jpskenn/Colice/assets/Colice_v.0.2_5.jpeg

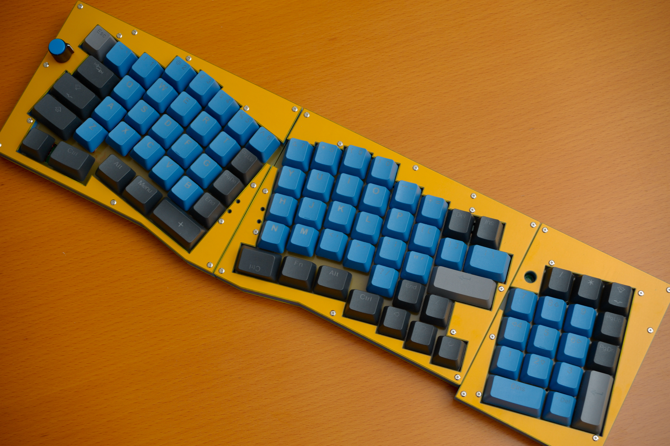
assets/Colice_v.0.2_5.jpeg
