jpskenn/Colice/assets/Colice_v.0.2_9.jpeg

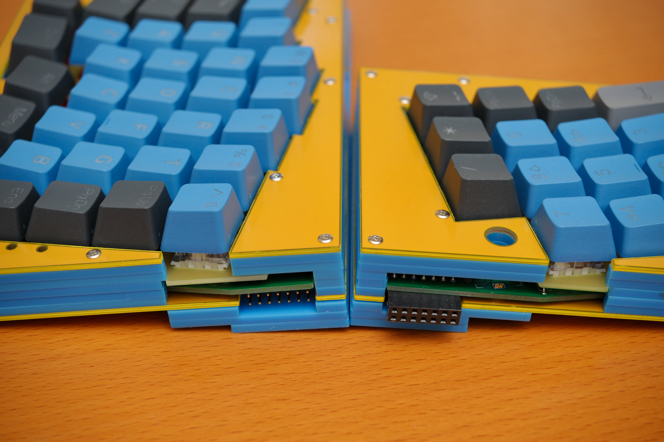
assets/Colice_v.0.2_9.jpeg
