jpskenn/Colice/assets/Colice_v.0.2_11.jpeg

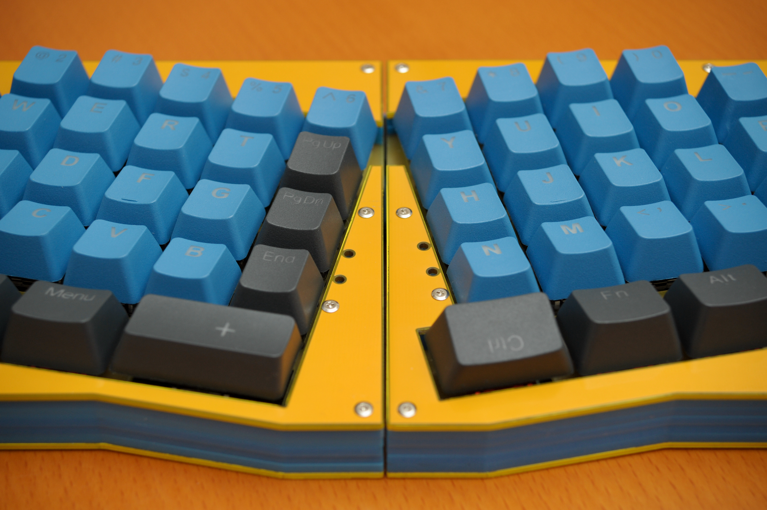
assets/Colice_v.0.2_11.jpeg
