jpskenn/Colice/idea/7w7xx1621ke41.jpg

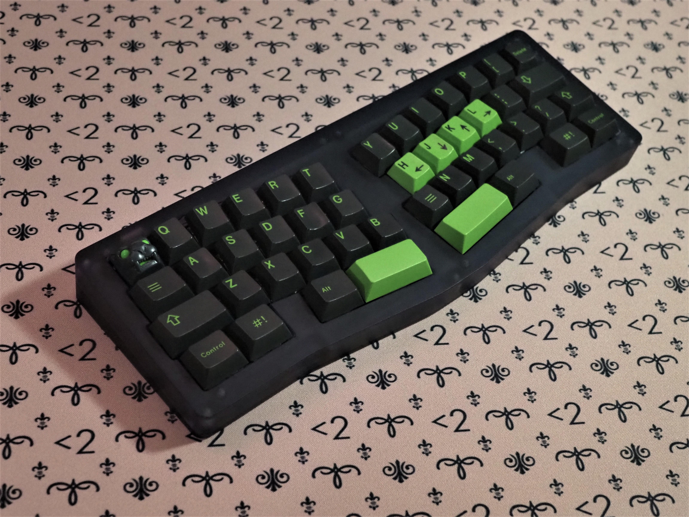
idea/7w7xx1621ke41.jpg
