jpskenn/Colice/idea/fullsizeoutput_168.jpeg

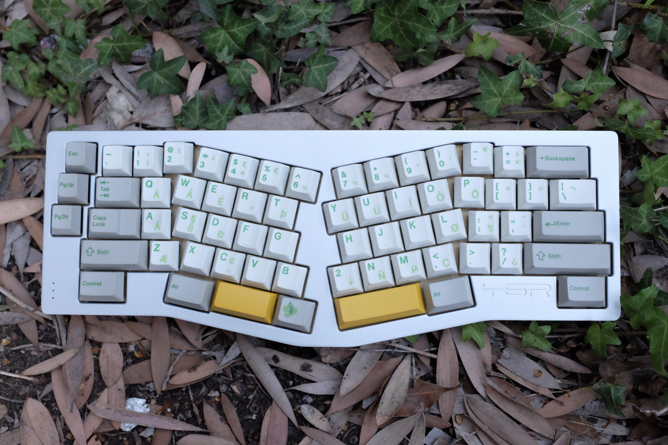
idea/fullsizeoutput_168.jpeg
