jpskenn/Colice/idea/IMG_0921.jpeg

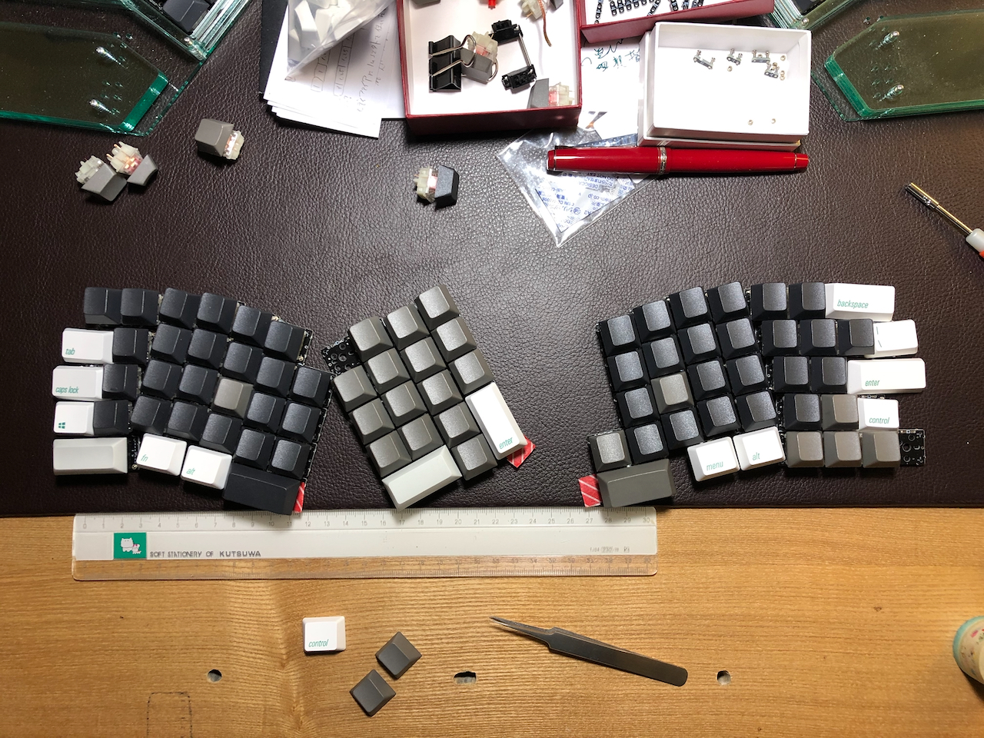
idea/IMG_0921.jpeg
