jpskenn/Colice/idea/IMG_0922.jpeg

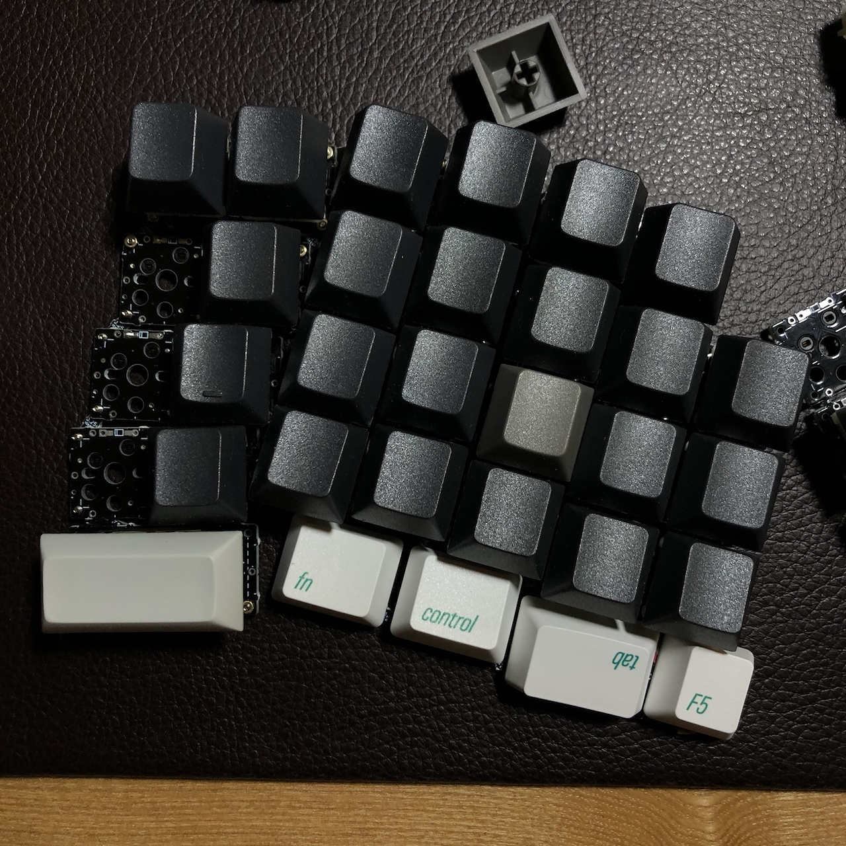
idea/IMG_0922.jpeg
