jpskenn/Colice/idea/keyboards_ergo_tgr-alice-layout-1024x415.png

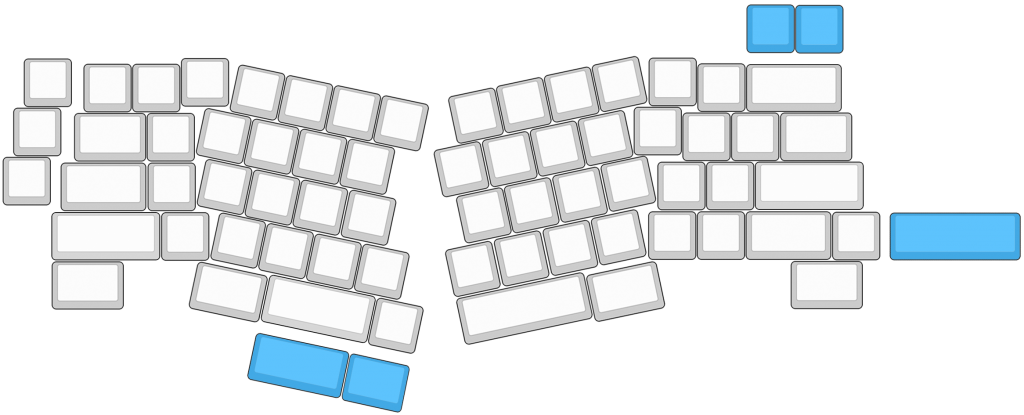
idea/keyboards_ergo_tgr-alice-layout-1024x415.png
