jpskenn/Colice/idea/Lain_by_hsgw.jpg

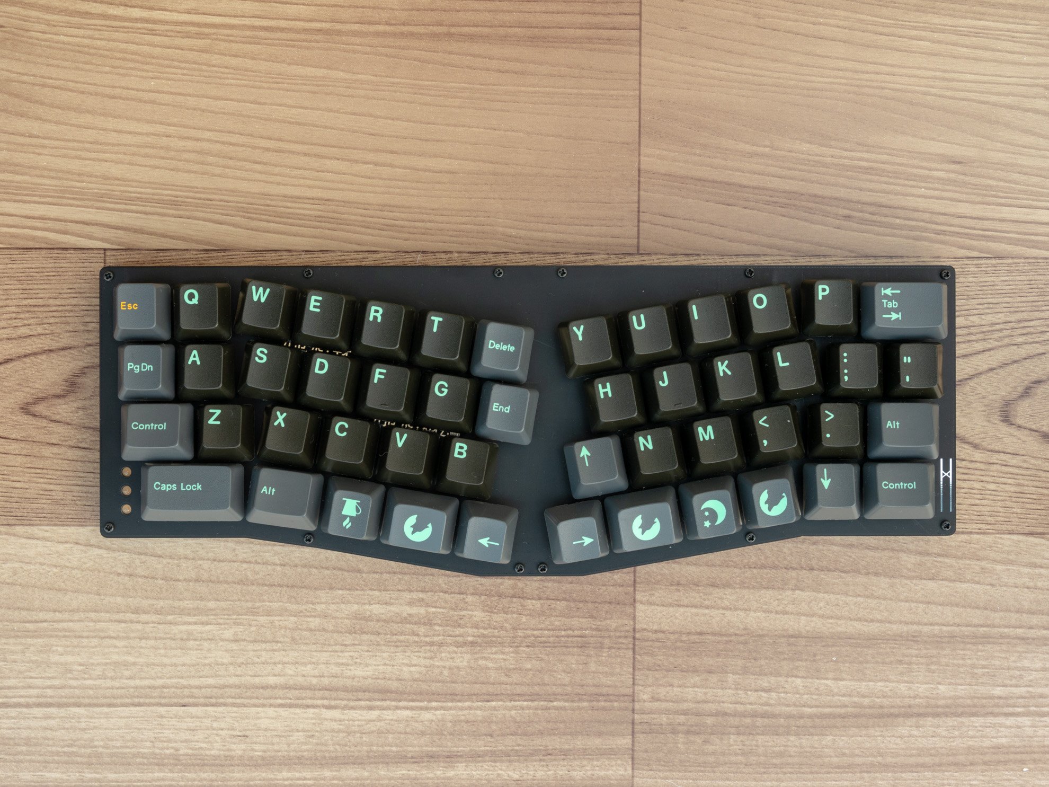
idea/Lain_by_hsgw.jpg
