jpskenn/Colice/idea/mainphoto.jpg

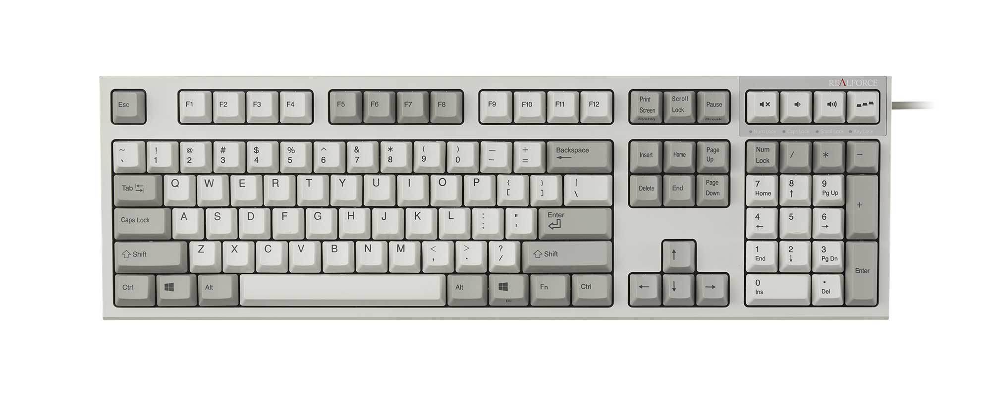
idea/mainphoto.jpg
