jpskenn/Colice/idea/uoq6nv9i2eb41 2.jpg

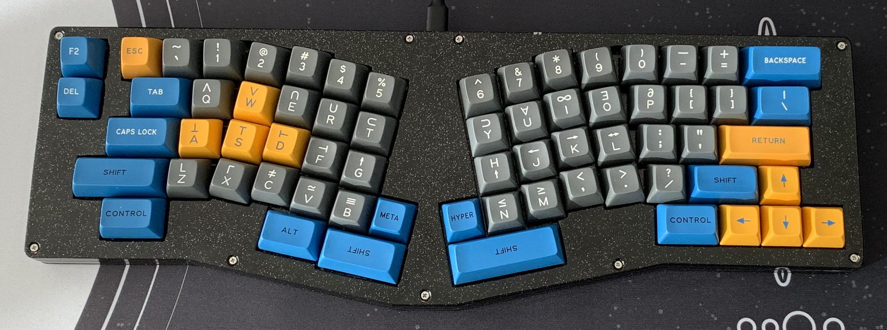
idea/uoq6nv9i2eb41 2.jpg
