jpskenn/Colice/idea/uoq6nv9i2eb41.jpg

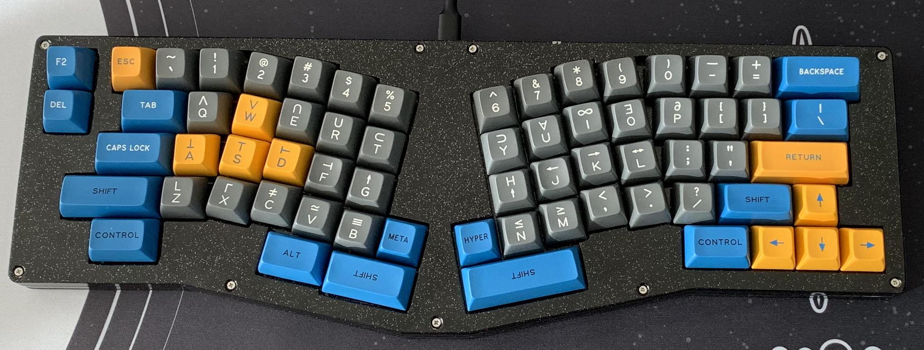
idea/uoq6nv9i2eb41.jpg
