jpskenn/Colice/idea/一体型分割3.jpg

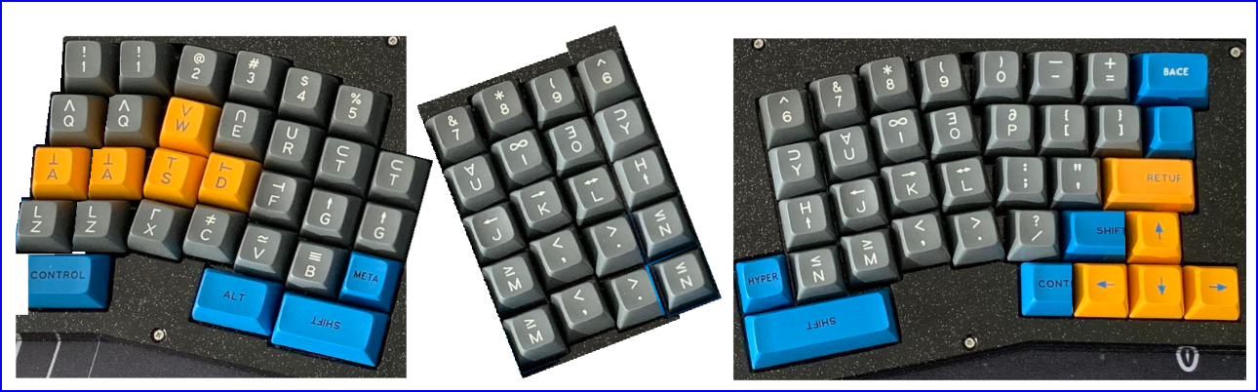
idea/一体型分割3.jpg
