jpskenn/Colice/PCB_Keyplate/v.0.1/left_keyplate2.dxf

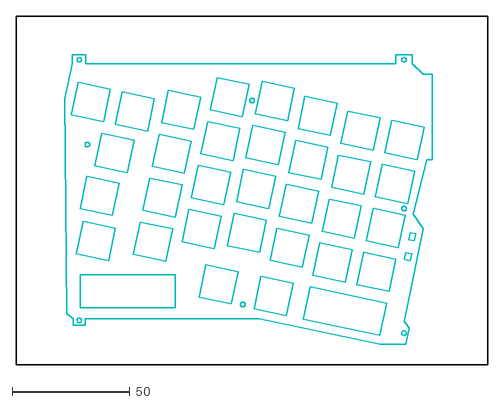
[picture p36: CAD file, 2025-01-15, an earlier design]
PCB_Keyplate/v.0.1/left_keyplate2.dxf
199.8 x 147.9
