jpskenn/Colice/PCB_MidFrame/v.0.1/left_mid.dxf

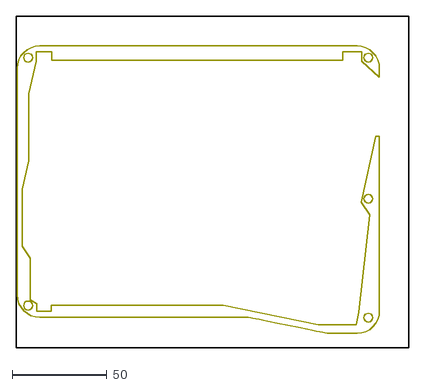
[picture p37: CAD file, 2025-01-15, an earlier design]
PCB_MidFrame/v.0.1/left_mid.dxf
207.4 x 175.2
