jpskenn/Colice/PCB_TopFrame/v.0.1/left_top2.dxf

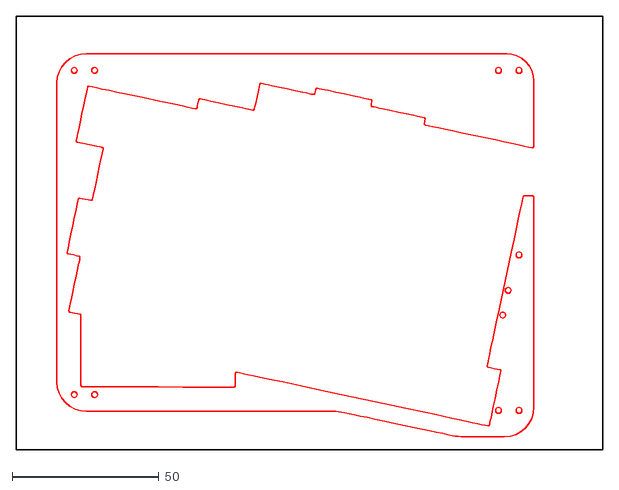
[picture p38: CAD file, 2025-01-15, an earlier design]
PCB_TopFrame/v.0.1/left_top2.dxf
199.8 x 147.9
