jpskenn/Colice/PCB_Bottom/v.0.1/left_bottom.dxf

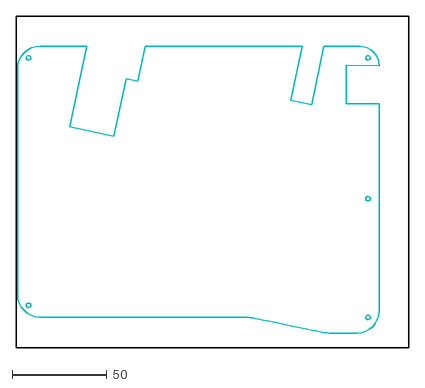
[picture p39: CAD file, 2025-01-15, an earlier design]
PCB_Bottom/v.0.1/left_bottom.dxf
207.4 x 175.2
