jpskenn/Colice/Case : Plate/3D Print/3dCase_test_2020-Feb-23_08-43-58AM-000_CustomizedView15799716209.png

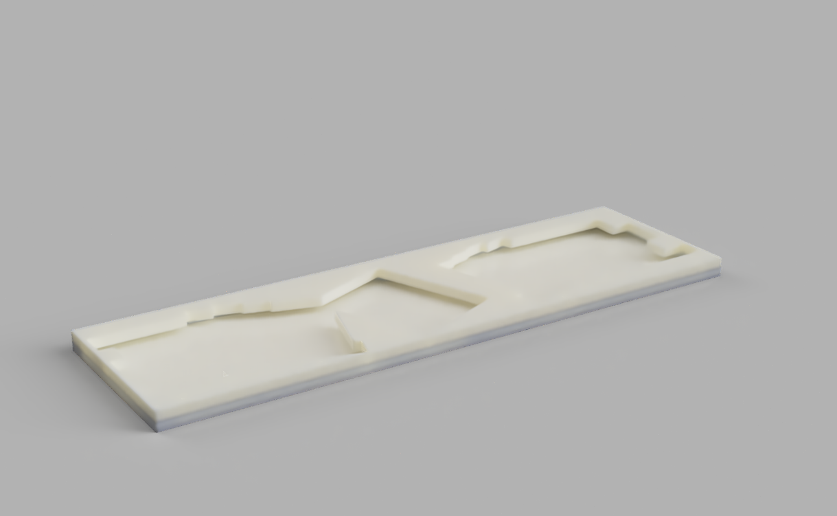
Case : Plate/3D Print/3dCase_test_2020-Feb-23_08-43-58AM-000_CustomizedView15799716209.png
