jpskenn/Colice/PCB/Num v.0.1/Colice_RR_Num_rev.0.1-003/Colice.kicad_pcb

## KiCad design PCB/Num v.0.1/Colice_RR_Num_rev.0.1-003/Colice.kicad_pcb (2025-01-15, an earlier design)

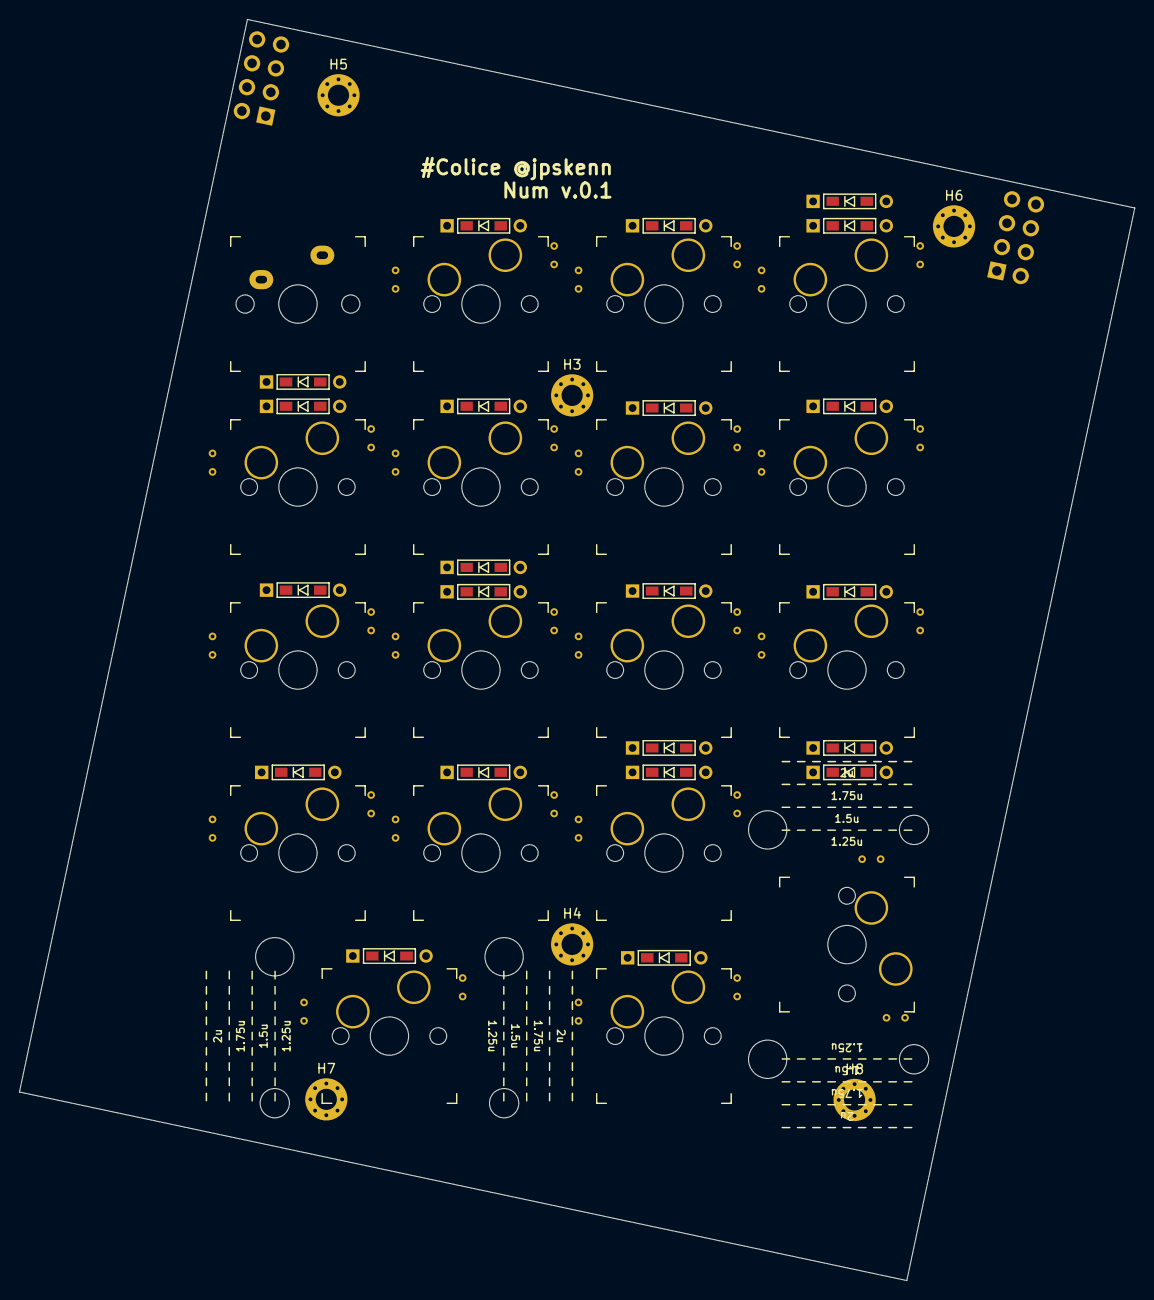
[picture p47: board PCB/Num v.0.1/Colice_RR_Num_rev.0.1-003/Colice.kicad_pcb from above]

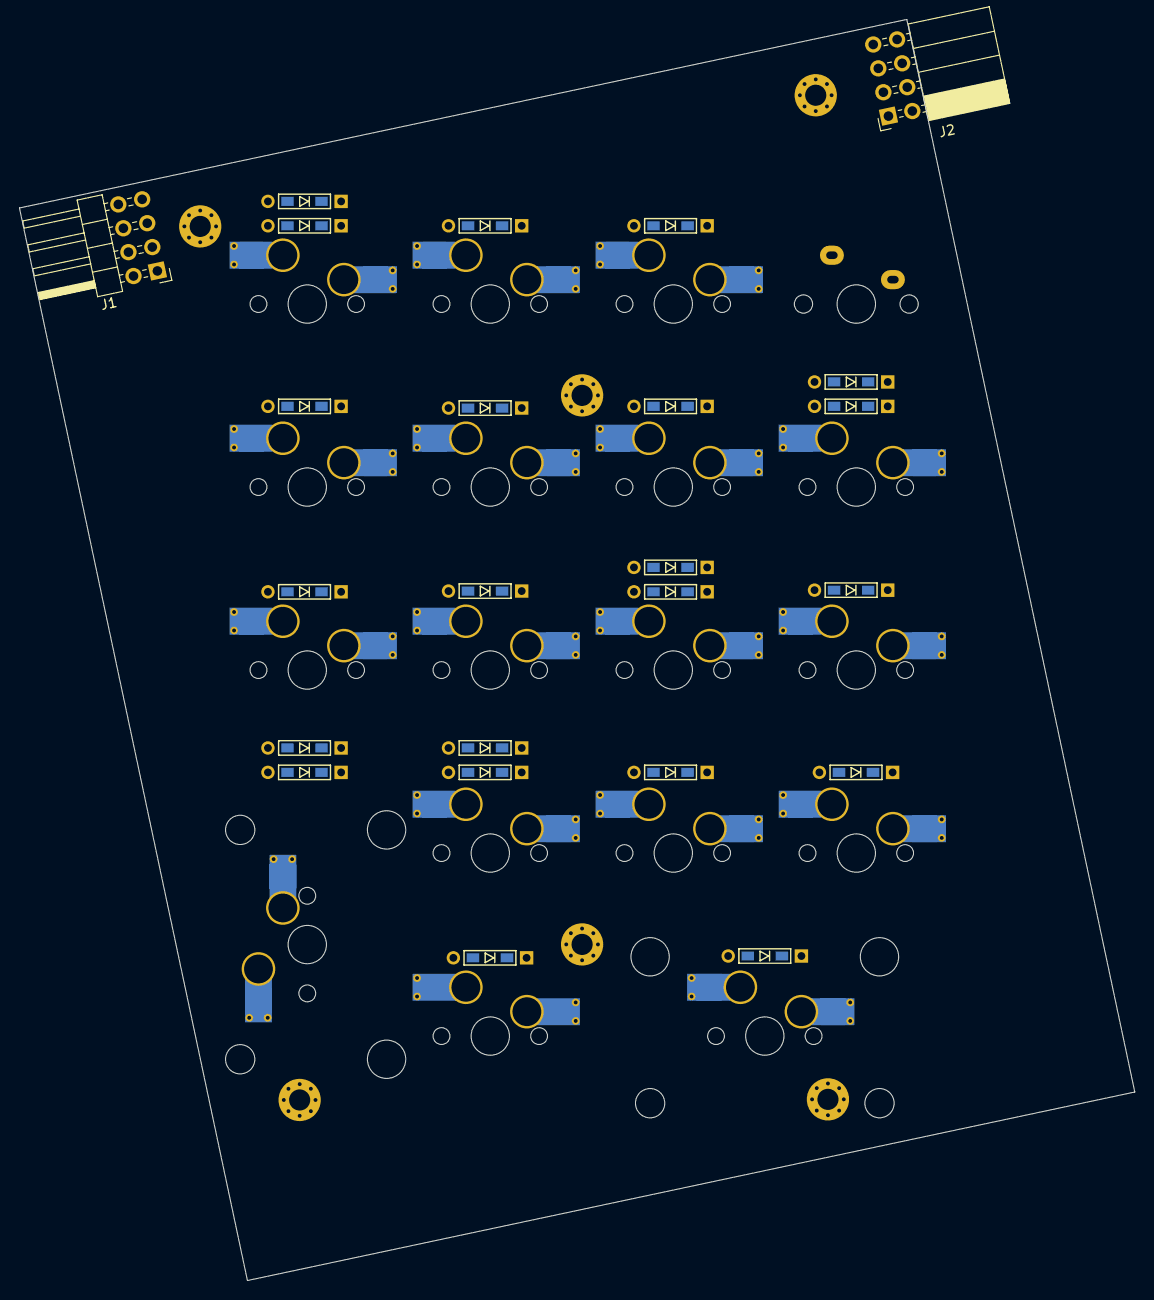
[picture p48: board PCB/Num v.0.1/Colice_RR_Num_rev.0.1-003/Colice.kicad_pcb from below]

Board: 2 copper layers, 116.1 x 131.3 mm, 50 parts (2 on the bottom side), 30 nets, no tracks yet.

Parts:
D1, D2, D3, D4, D5, D6, D7, D8, D9, D10, D11, D12, D13, D14, D15, D16, D17, D18, D19, D20, D21, D22: D; D3_TH_SMD
H1, H2: MountingHole; CherryMX_MidHeight_Choc_Hotswap_2U_Outline
H3, H4, H5, H6, H7, H8: MountingHole; MountingHole_2.2mm_M2_Pad_Via
J1: Conn_02x04_Counter_Clockwise; PinHeader_2x04_P2.54mm_Horizontal
J2: Conn_02x04_Counter_Clockwise; PinSocket_2x04_P2.54mm_Horizontal
SW1: SW_PUSH; CherryMX_1u
SW1#2, SW2, SW3, SW4, SW5, SW6, SW7, SW8, SW9, SW10, SW11, SW12, SW13, SW14, SW15, SW16, SW17: SW_Push; CherryMX_Hotswap_v2

Connections:
GND: J1.7, J2.7
unnamed: D1.2, SW1#2.2
unnamed: D2.2, SW2.2
unnamed: D3.2, SW3.2
unnamed: D4.2, SW4.2
unnamed: D5.2, SW5.2
unnamed: D6.2, SW6.2
unnamed: D7.2, SW7.2
unnamed: D8.2, SW8.2
unnamed: D9.2, SW9.2
unnamed: D10.2, SW10.2
unnamed: D11.2, SW11.2
unnamed: D12.2, SW12.2
unnamed: D13.2, SW13.2
unnamed: D14.2, SW14.2
unnamed: D15.2, SW15.2
unnamed: D16.2, SW16.2
unnamed: D17.2, SW17.2
unnamed: D18.1, SW14.1, SW15.1, SW16.1
unnamed: D19.1, SW1#2.1, SW2.1, SW3.1, SW4.1
unnamed: D20.1, SW7.1, SW8.1
unnamed: D21.1, SW5.1, SW6.1, SW12.1, SW13.1
unnamed: D22.1, SW9.1, SW10.1, SW11.1, SW17.1
VCC: J1.8, J2.8
data: J1.6, J2.6
pin6: D5.1, D9.1, D14.1, D19.2, J2.1
pin7: D1.1, D6.1, D10.1, D15.1, D20.2, J2.2
pin8: D2.1, D7.1, D11.1, D16.1, D21.2, J2.3
pin9: D3.1, D8.1, D12.1, D22.2, J2.4
pin10: D4.1, D13.1, D17.1, D18.2, J2.5
