jpskenn/Colice/PCB/Colice_rev.0.1/Colice_rev.0.1.kicad_pcb

## KiCad design PCB/Colice_rev.0.1/Colice_rev.0.1.kicad_pcb (2025-01-15)

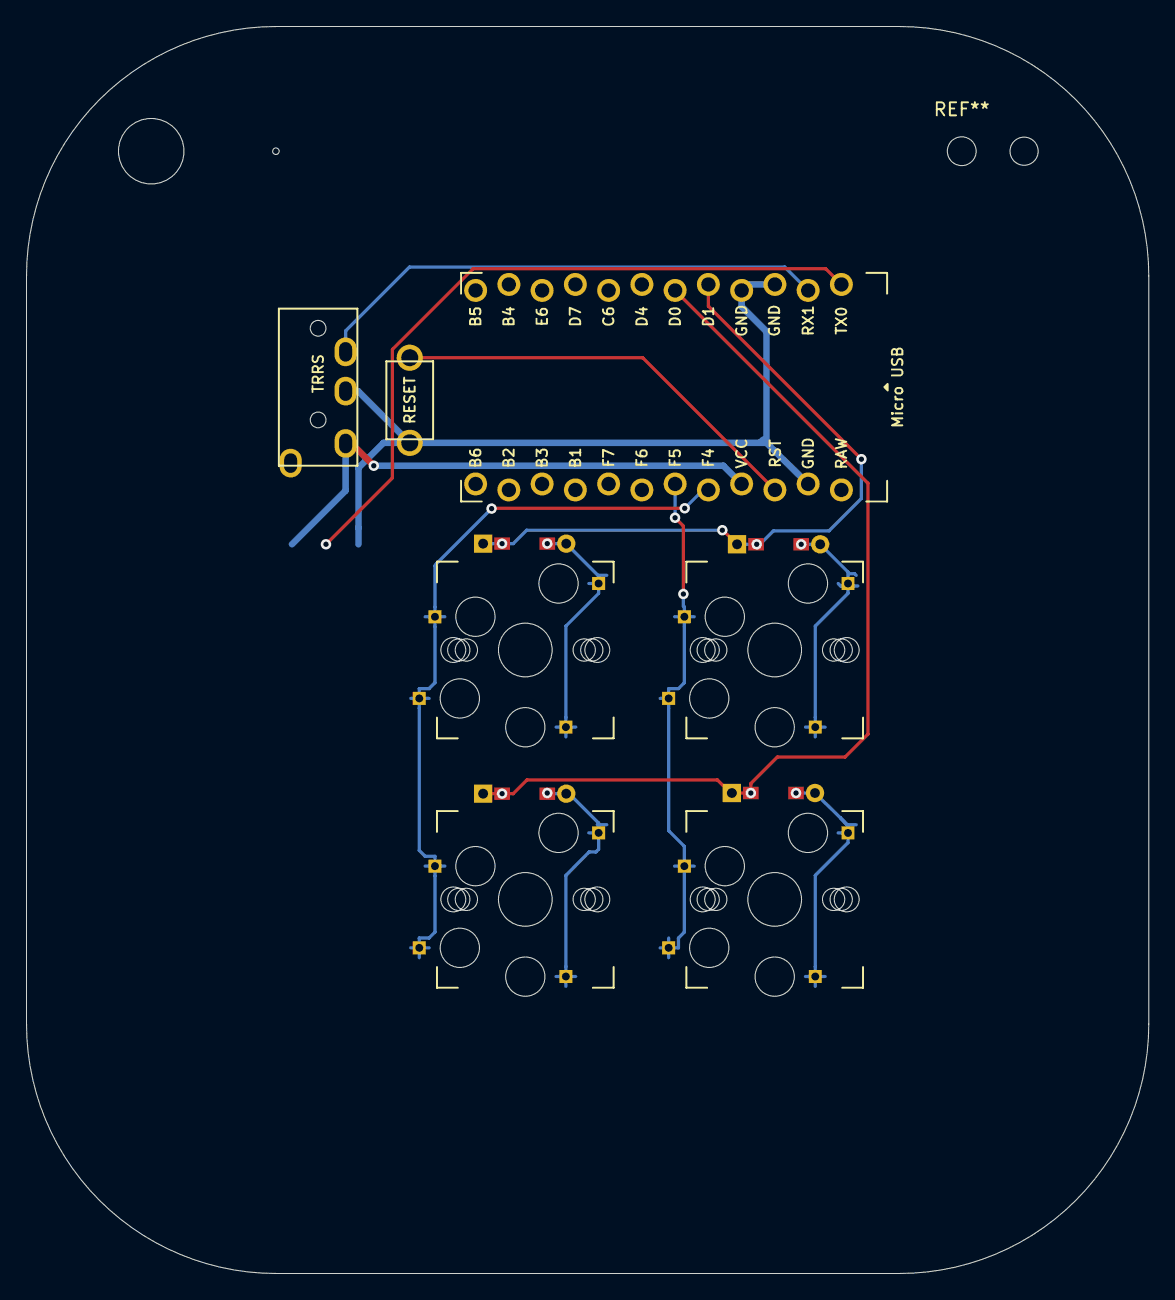
[picture p49: board Colice_rev.0.1.kicad_pcb from above]

Board: 2 copper layers, 85.7 x 95.2 mm, 13 parts (0 on the bottom side), 13 nets.

Parts:
D1, D2, D3, D4: D; diode_TH_SMD_rev2
J1: MJ-4PP-9
J2: LED; StripLED_rev2
Ref**: Val**; IM_HOLE
SW1: SW_Push; ResetSW
SW2, SW3, SW4, SW5: SW_Push; CherryMX_MidHeight_Choc_Hotswap_rev5
U1: pro_micro; ArduinoProMicro-ZigZag_rev5

Connections:
GND: J1.C, J2.1, SW1.2, U1.3, U1.4, U1.23
unnamed: D1.2, SW2.2
unnamed: D2.2, SW3.2
unnamed: D3.2, SW4.2
unnamed: D4.2, SW5.2
VCC: J1.D, J2.3, U1.21
col0: SW2.1, SW3.1, U1.20
col1: SW4.1, SW5.1, U1.19
data: J1.B, U1.2
led: J2.2, U1.1
reset: SW1.1, U1.22
row0: D1.1, D3.1, U1.5
row1: D2.1, D4.1, U1.6
