jpskenn/Colice/PCB/Num v.0.2/Colice_RR_Num_rev.0.2-001/Colice.kicad_pcb

## KiCad design PCB/Num v.0.2/Colice_RR_Num_rev.0.2-001/Colice.kicad_pcb (2025-01-15)

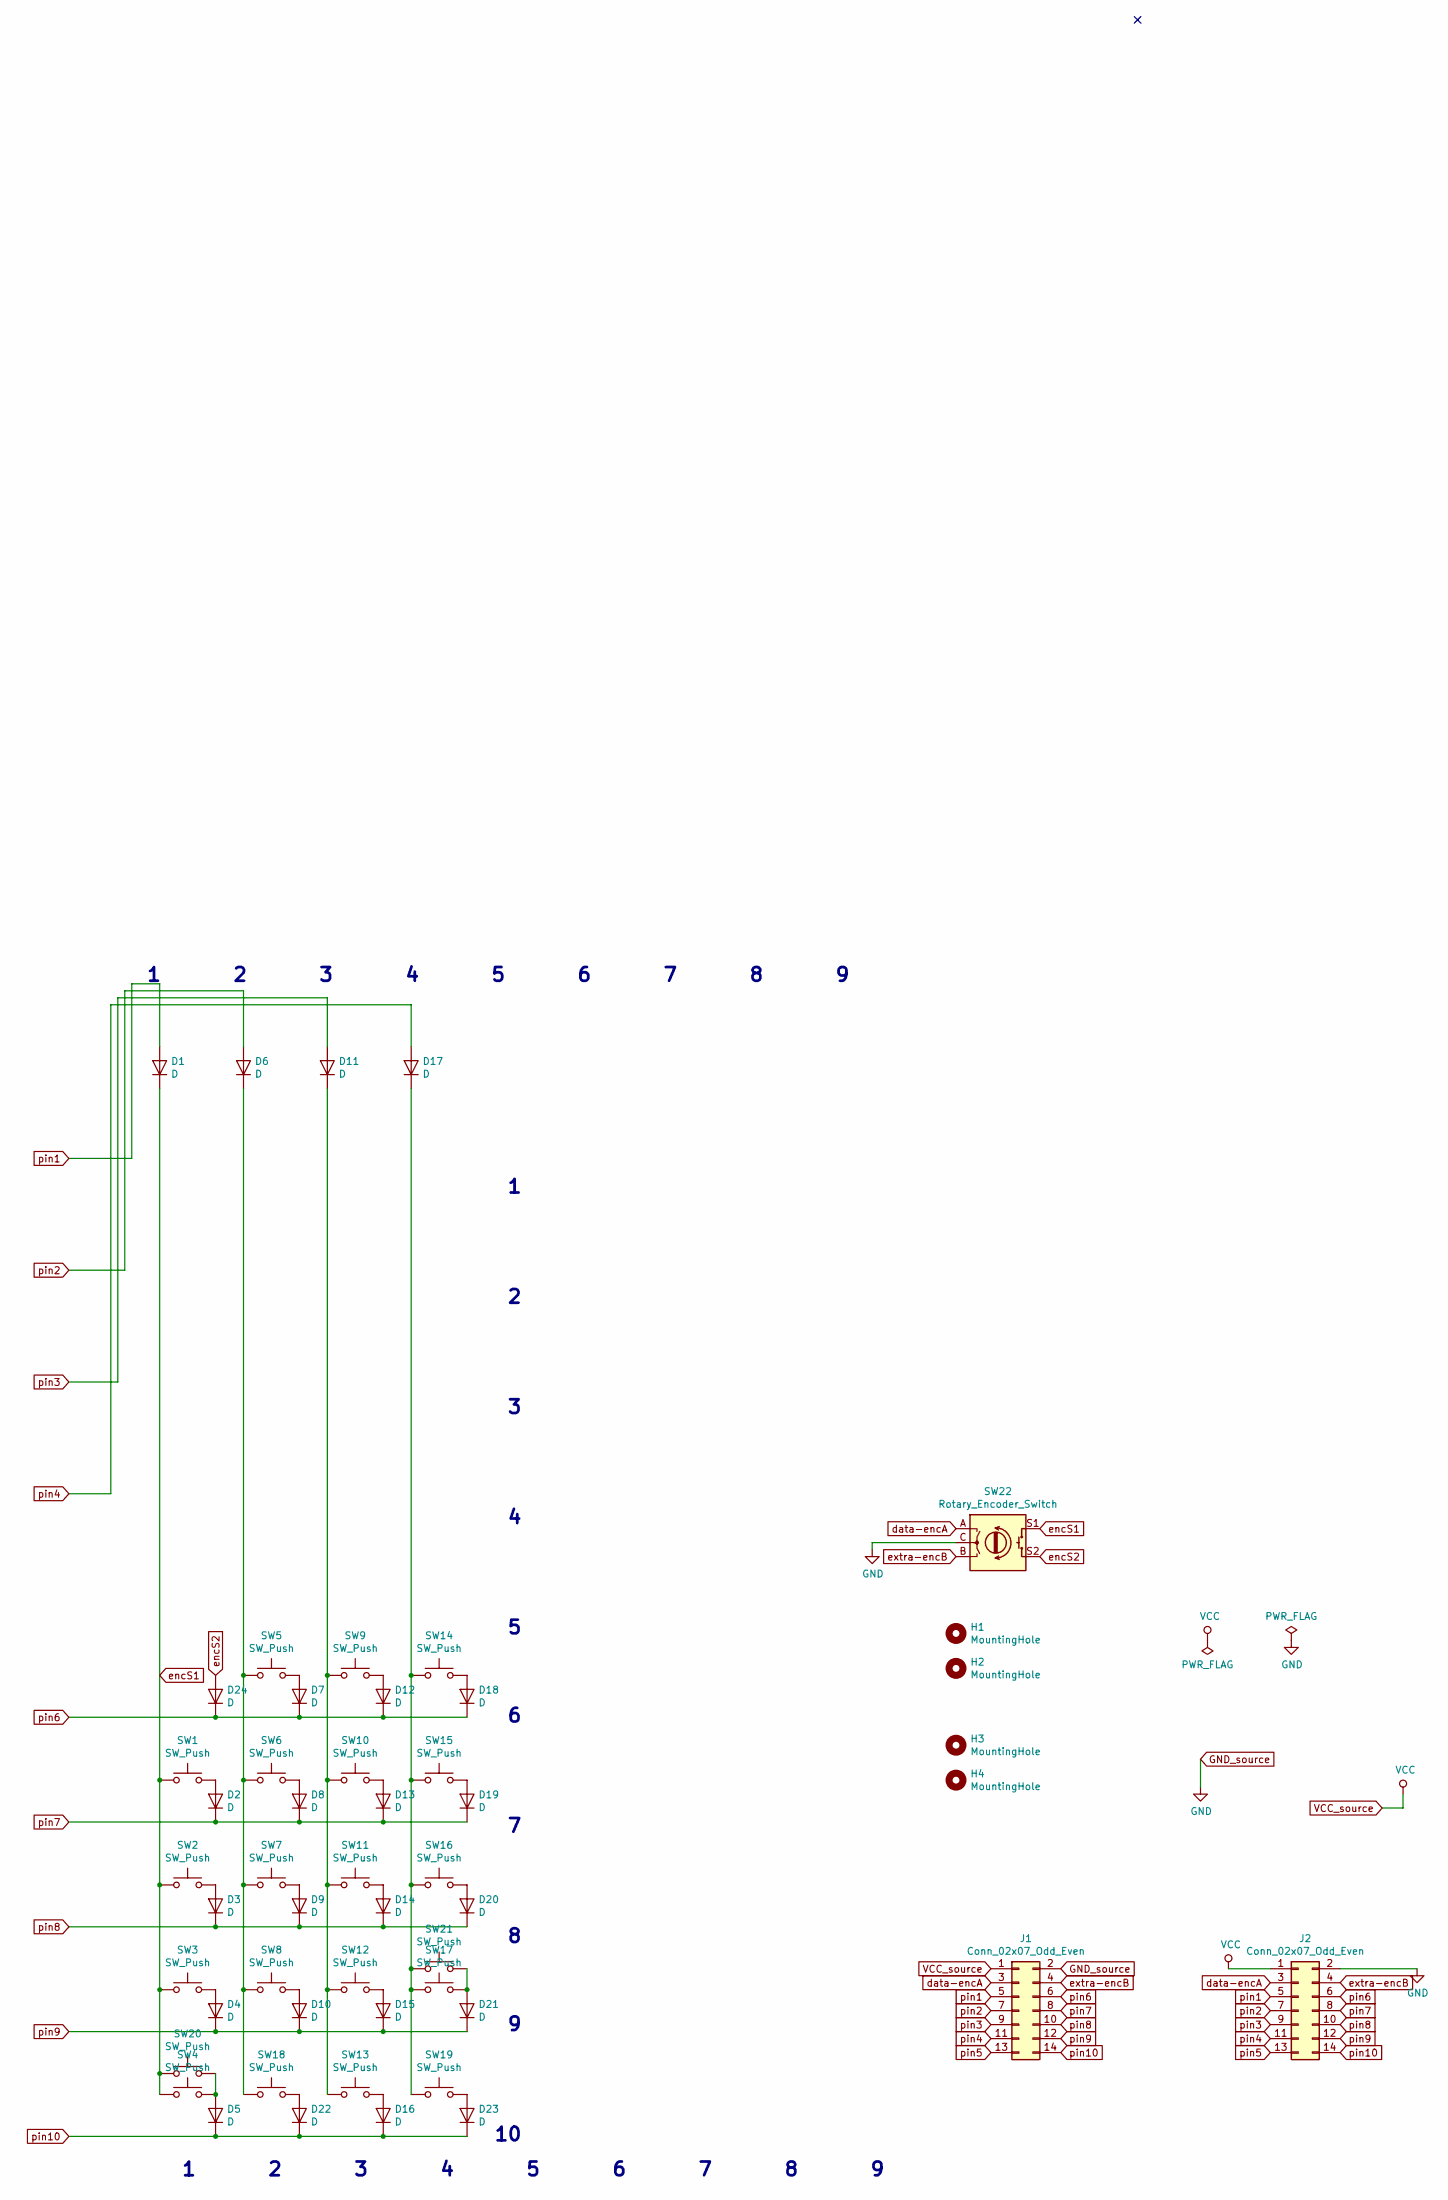
[picture p50: schematic Colice.sch]

Parts:
D1, D2, D3, D4, D5, D6, D7, D8, D9, D10, D11, D12, D13, D14, D15, D16, D17, D18, D19, D20, D21, D22, D23, D24: D; D3_TH_SMD
H1, H2: MountingHole; CherryMX_MidHeight_Choc_Hotswap_2U_Outline
H3, H4: MountingHole; MountingHole_2.2mm_M2_Pad_Via
J1: Conn_02x07_Odd_Even; PinSocket_2x07_P2.54mm_Horizontal
J2: Conn_02x07_Odd_Even; PinHeader_2x07_P2.54mm_Horizontal
SW1, SW2, SW3, SW4, SW5, SW6, SW7, SW8, SW9, SW10, SW11, SW12, SW13, SW14, SW15, SW16, SW17, SW18, SW19, SW20, SW21: SW_Push; CherryMX_Hotswap_v2
SW22: Rotary_Encoder_Switch; RotaryEncoder_Alps_EC11E-Switch_Vertical_H20mm_rev2

Connections:
GND_source: J1.2, J2.2, SW22.C
unnamed: D2.2 (A), SW1.2
unnamed: D3.2 (A), SW2.2
unnamed: D4.2 (A), SW3.2
unnamed: D5.2 (A), SW4.2, SW20.2
unnamed: D6.1 (K), SW5.1, SW6.1, SW7.1, SW8.1, SW18.1
unnamed: D7.2 (A), SW5.2
unnamed: D8.2 (A), SW6.2
unnamed: D9.2 (A), SW7.2
unnamed: D10.2 (A), SW8.2
unnamed: D11.1 (K), SW9.1, SW10.1, SW11.1, SW12.1, SW13.1
unnamed: D12.2 (A), SW9.2
unnamed: D13.2 (A), SW10.2
unnamed: D14.2 (A), SW11.2
unnamed: D15.2 (A), SW12.2
unnamed: D16.2 (A), SW13.2
unnamed: D17.1 (K), SW14.1, SW15.1, SW16.1, SW17.1, SW19.1, SW21.1
unnamed: D18.2 (A), SW14.2
unnamed: D19.2 (A), SW15.2
unnamed: D20.2 (A), SW16.2
unnamed: D21.2 (A), SW17.2, SW21.2
unnamed: D22.2 (A), SW18.2
unnamed: D23.2 (A), SW19.2
VCC_source: J1.1, J2.1
data-encA: J1.3, J2.3, SW22.A
encS1: D1.1 (K), SW1.1, SW2.1, SW3.1, SW4.1, SW20.1, SW22.S1
encS2: D24.2 (A), SW22.S2
extra-encB: J1.4, J2.4, SW22.B
pin1: D1.2 (A), J1.5, J2.5
pin2: D6.2 (A), J1.7, J2.7
pin3: D11.2 (A), J1.9, J2.9
pin4: D17.2 (A), J1.11, J2.11
pin5: J1.13, J2.13
pin6: D7.1 (K), D12.1 (K), D18.1 (K), D24.1 (K), J1.6, J2.6
pin7: D2.1 (K), D8.1 (K), D13.1 (K), D19.1 (K), J1.8, J2.8
pin8: D3.1 (K), D9.1 (K), D14.1 (K), D20.1 (K), J1.10, J2.10
pin9: D4.1 (K), D10.1 (K), D15.1 (K), D21.1 (K), J1.12, J2.12
pin10: D5.1 (K), D16.1 (K), D22.1 (K), D23.1 (K), J1.14, J2.14

Notes on the sheet:
1 2 3 4 5 6 7 8 9
1 2 3 4 5 6 7 8 9 10

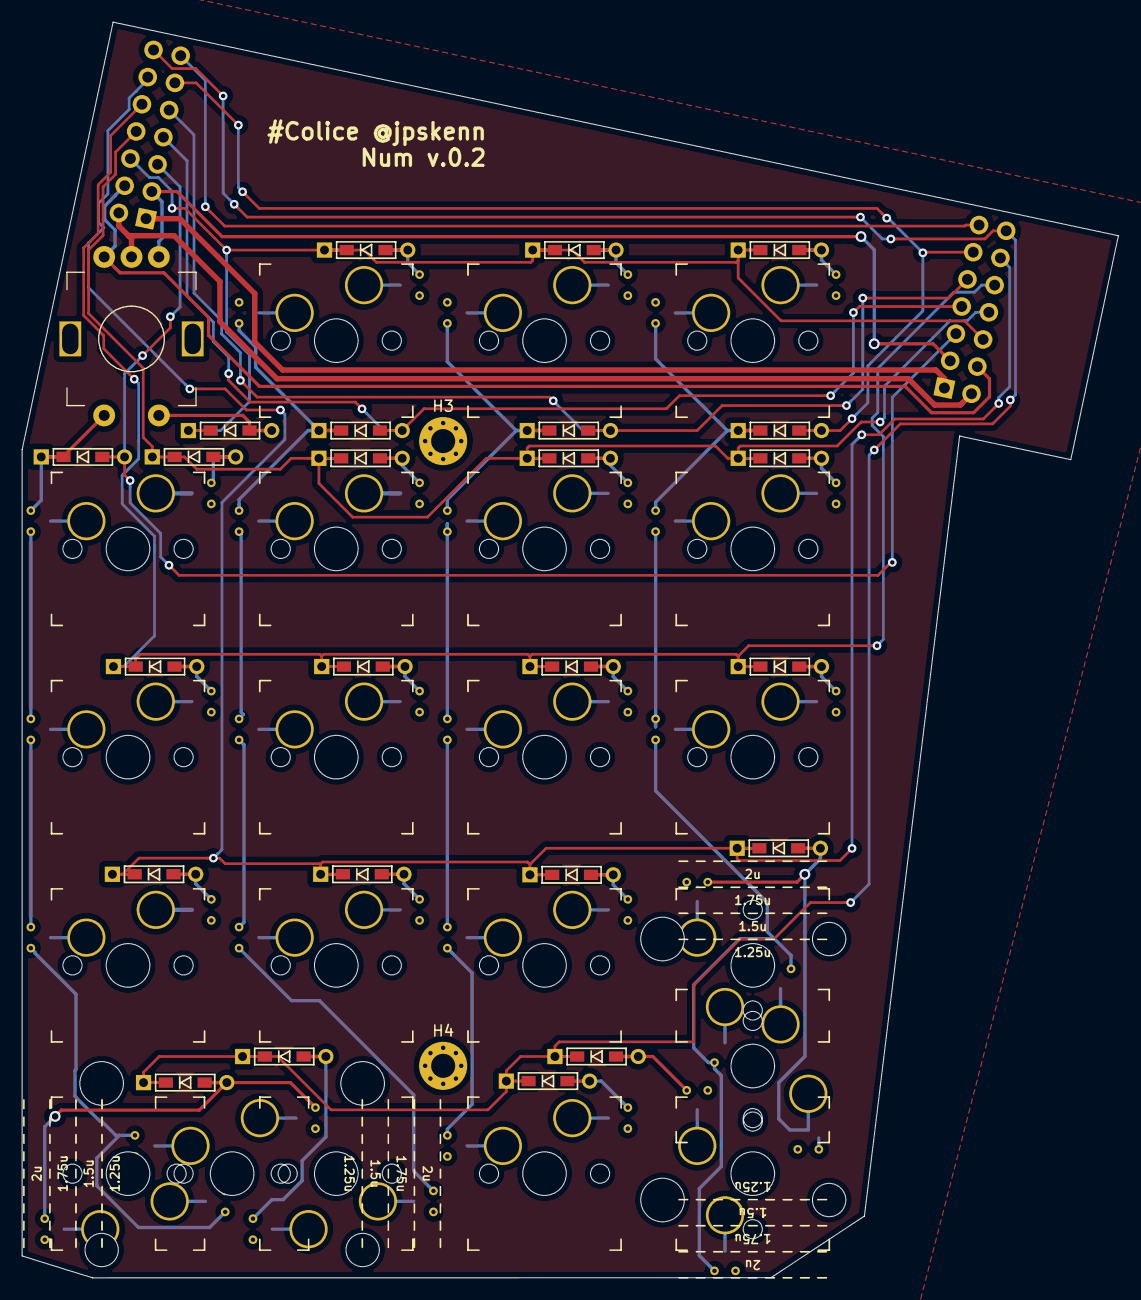
[picture p51: board PCB/Num v.0.2/Colice_RR_Num_rev.0.2-001/Colice.kicad_pcb from above]

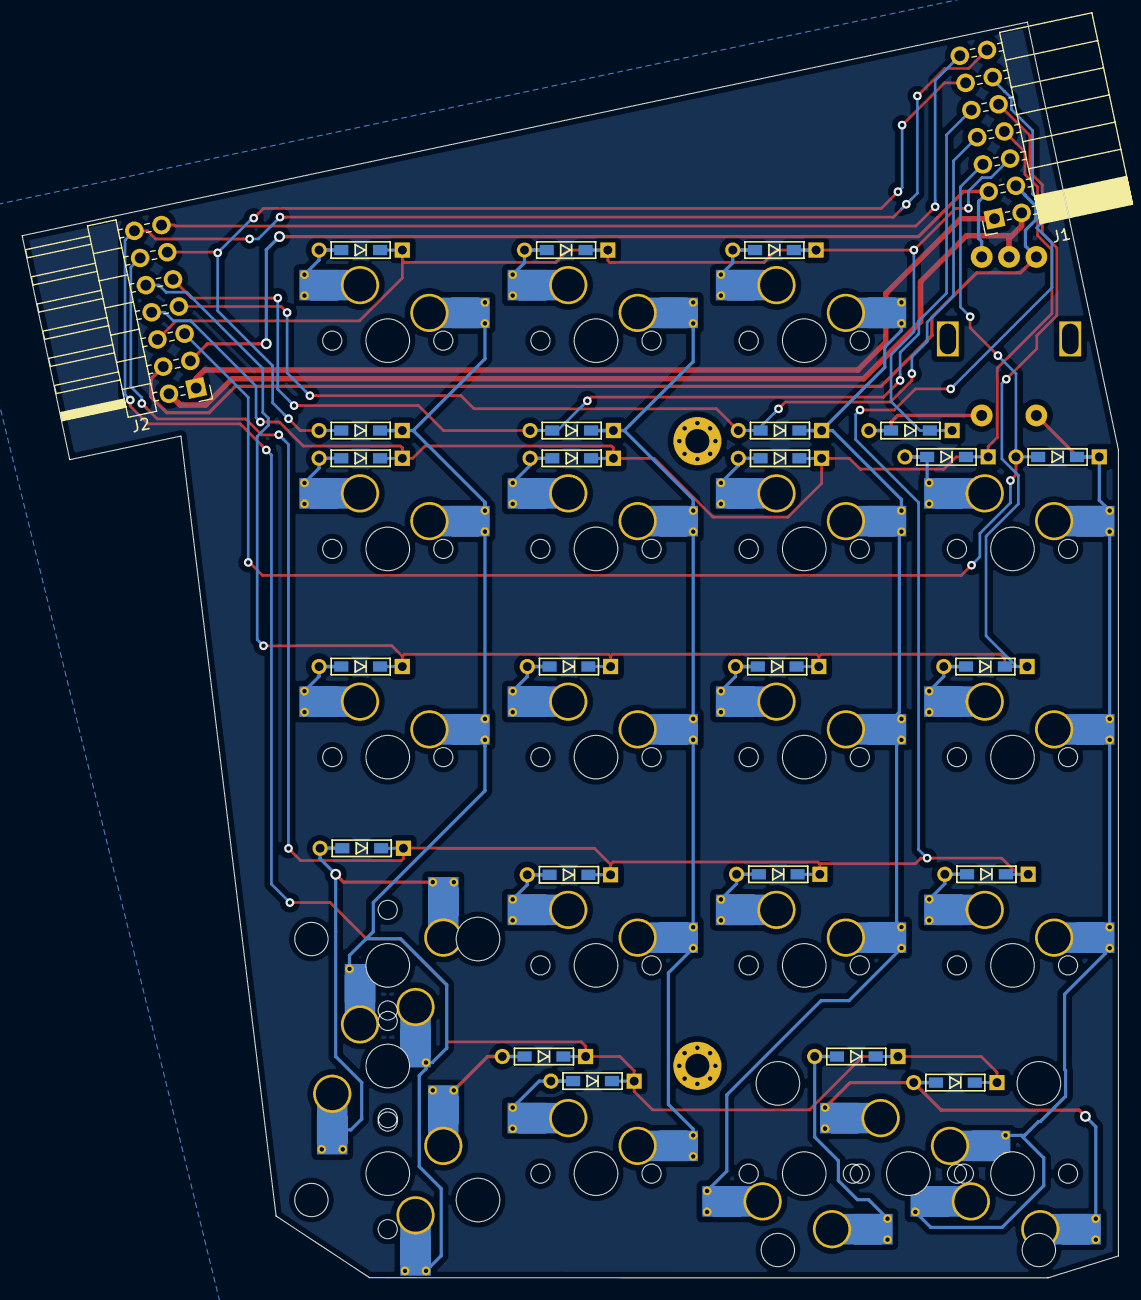
[picture p52: board PCB/Num v.0.2/Colice_RR_Num_rev.0.2-001/Colice.kicad_pcb from below]

Board: 2 copper layers, 100.3 x 114.9 mm, 52 parts (2 on the bottom side), 38 nets.
