jpskenn/Colice/PCB/Left v.0.1/Colice_RR_rev.0.11/Colice.kicad_pcb

## KiCad design PCB/Left v.0.1/Colice_RR_rev.0.11/Colice.kicad_pcb (2025-01-15, an earlier design)

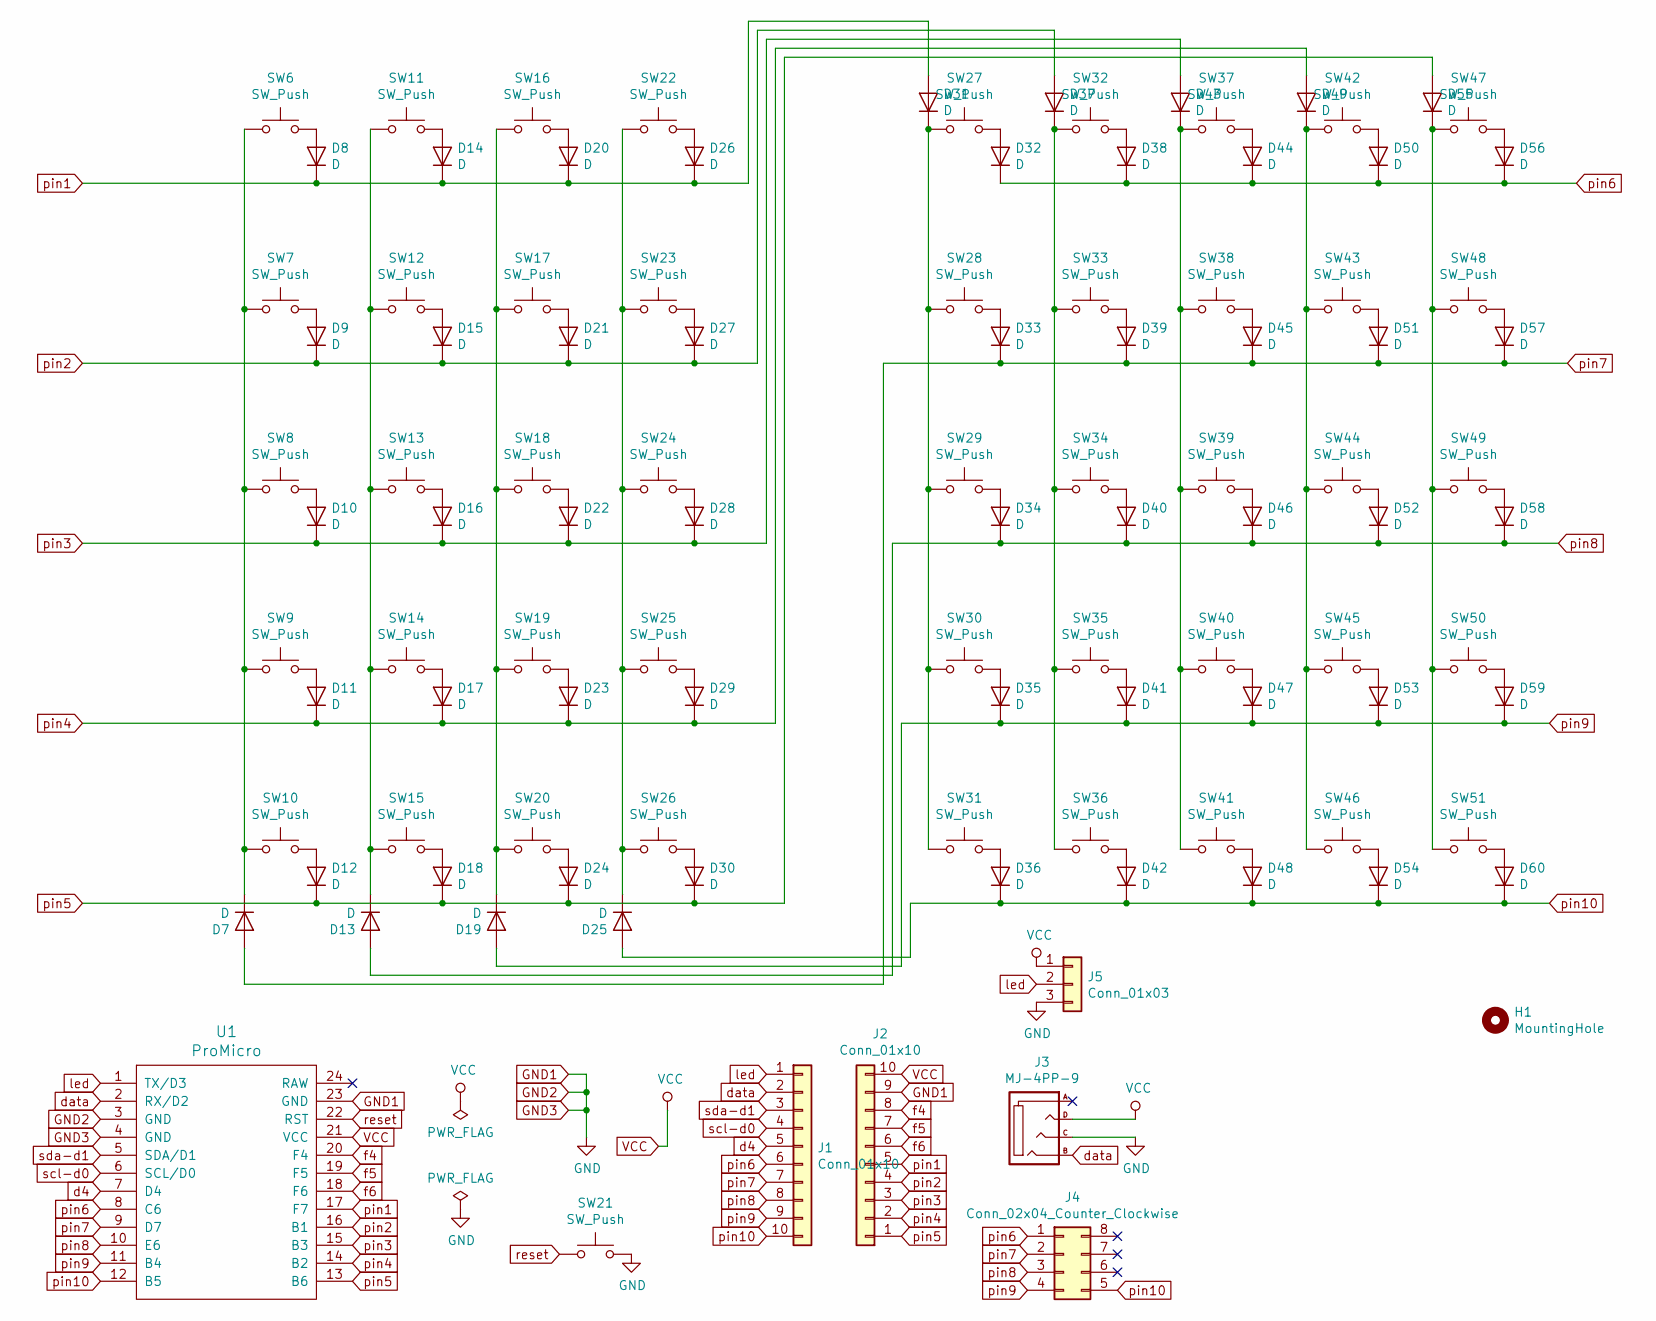
[picture p53: schematic Colice.sch]

Parts:
D7, D8, D9, D10, D11, D12, D13, D14, D15, D16, D17, D18, D19, D20, D21, D22, D23, D24, D25, D26, D27, D28, D29, D30, D31, D32, D33, D34, D35, D36, D37, D38, D39, D40, D41, D42, D43, D44, D45, D46, D47, D48, D49, D50, D51, D52, D53, D54, D55, D56, D57, D58, D59, D60: D; D3_TH_SMD
H1: MountingHole; CherryMX_MidHeight_Choc_Hotswap_2.25U_Outline
J1, J2: Conn_01x10; PinHeader_1x10_P2.54mm_Vertical
J3: MJ-4PP-9
J4: Conn_02x04_Counter_Clockwise; PinSocket_2x04_P2.54mm_Horizontal
J5: Conn_01x03; Pin_Header_Straight_1x03
SW6, SW7, SW8, SW9, SW10, SW11, SW12, SW13, SW14, SW15, SW16, SW17, SW18, SW19, SW20, SW22, SW23, SW24, SW25, SW26, SW27, SW28, SW29, SW30, SW31, SW32, SW33, SW34, SW35, SW36, SW37, SW38, SW39, SW40, SW41, SW42, SW43, SW44, SW45, SW46, SW47, SW48, SW49, SW50, SW51: SW_Push; CherryMX_Hotswap_v2
SW21: SW_Push; ResetSW
U1: ProMicro

Connections:
GND1: J2.9, J3.C, J5.3, SW21.2, U1.3 (GND), U1.4 (GND), U1.23 (GND)
unnamed: D7.1 (K), SW6.1, SW7.1, SW8.1, SW9.1, SW10.1
unnamed: D8.2 (A), SW6.2
unnamed: D9.2 (A), SW7.2
unnamed: D10.2 (A), SW8.2
unnamed: D11.2 (A), SW9.2
unnamed: D12.2 (A), SW10.2
unnamed: D13.1 (K), SW11.1, SW12.1, SW13.1, SW14.1, SW15.1
unnamed: D14.2 (A), SW11.2
unnamed: D15.2 (A), SW12.2
unnamed: D16.2 (A), SW13.2
unnamed: D17.2 (A), SW14.2
unnamed: D18.2 (A), SW15.2
unnamed: D19.1 (K), SW16.1, SW17.1, SW18.1, SW19.1, SW20.1
unnamed: D20.2 (A), SW16.2
unnamed: D21.2 (A), SW17.2
unnamed: D22.2 (A), SW18.2
unnamed: D23.2 (A), SW19.2
unnamed: D24.2 (A), SW20.2
unnamed: D25.1 (K), SW22.1, SW23.1, SW24.1, SW25.1, SW26.1
unnamed: D26.2 (A), SW22.2
unnamed: D27.2 (A), SW23.2
unnamed: D28.2 (A), SW24.2
unnamed: D29.2 (A), SW25.2
unnamed: D30.2 (A), SW26.2
unnamed: D31.1 (K), SW27.1, SW28.1, SW29.1, SW30.1, SW31.1
unnamed: D32.2 (A), SW27.2
unnamed: D33.2 (A), SW28.2
unnamed: D34.2 (A), SW29.2
unnamed: D35.2 (A), SW30.2
unnamed: D36.2 (A), SW31.2
unnamed: D37.1 (K), SW32.1, SW33.1, SW34.1, SW35.1, SW36.1
unnamed: D38.2 (A), SW32.2
unnamed: D39.2 (A), SW33.2
unnamed: D40.2 (A), SW34.2
unnamed: D41.2 (A), SW35.2
unnamed: D42.2 (A), SW36.2
unnamed: D43.1 (K), SW37.1, SW38.1, SW39.1, SW40.1, SW41.1
unnamed: D44.2 (A), SW37.2
unnamed: D45.2 (A), SW38.2
unnamed: D46.2 (A), SW39.2
unnamed: D47.2 (A), SW40.2
unnamed: D48.2 (A), SW41.2
unnamed: D49.1 (K), SW42.1, SW43.1, SW44.1, SW45.1, SW46.1
unnamed: D50.2 (A), SW42.2
unnamed: D51.2 (A), SW43.2
unnamed: D52.2 (A), SW44.2
unnamed: D53.2 (A), SW45.2
unnamed: D54.2 (A), SW46.2
unnamed: D55.1 (K), SW47.1, SW48.1, SW49.1, SW50.1, SW51.1
unnamed: D56.2 (A), SW47.2
unnamed: D57.2 (A), SW48.2
unnamed: D58.2 (A), SW49.2
unnamed: D59.2 (A), SW50.2
unnamed: D60.2 (A), SW51.2
VCC: J2.10, J3.D, J5.1, U1.21 (VCC)
d4: J1.5, U1.7 (D4)
data: J1.2, J3.B, U1.2 (RX/D2)
f4: J2.8, U1.20 (F4)
f5: J2.7, U1.19 (F5)
f6: J2.6, U1.18 (F6)
led: J1.1, J5.2, U1.1 (TX/D3)
pin1: D8.1 (K), D14.1 (K), D20.1 (K), D26.1 (K), D31.2 (A), J2.5, U1.17 (F7)
pin2: D9.1 (K), D15.1 (K), D21.1 (K), D27.1 (K), D37.2 (A), J2.4, U1.16 (B1)
pin3: D10.1 (K), D16.1 (K), D22.1 (K), D28.1 (K), D43.2 (A), J2.3, U1.15 (B3)
pin4: D11.1 (K), D17.1 (K), D23.1 (K), D29.1 (K), D49.2 (A), J2.2, U1.14 (B2)
pin5: D12.1 (K), D18.1 (K), D24.1 (K), D30.1 (K), D55.2 (A), J2.1, U1.13 (B6)
pin6: D32.1 (K), D38.1 (K), D44.1 (K), D50.1 (K), D56.1 (K), J1.6, J4.1, U1.8 (C6)
pin7: D7.2 (A), D33.1 (K), D39.1 (K), D45.1 (K), D51.1 (K), D57.1 (K), J1.7, J4.2, U1.9 (D7)
pin8: D13.2 (A), D34.1 (K), D40.1 (K), D46.1 (K), D52.1 (K), D58.1 (K), J1.8, J4.3, U1.10 (E6)
pin9: D19.2 (A), D35.1 (K), D41.1 (K), D47.1 (K), D53.1 (K), D59.1 (K), J1.9, J4.4, U1.11 (B4)
pin10: D25.2 (A), D36.1 (K), D42.1 (K), D48.1 (K), D54.1 (K), D60.1 (K), J1.10, J4.5, U1.12 (B5)
reset: SW21.1, U1.22 (RST)
scl-d0: J1.4, U1.6 (SCL/D0)
sda-d1: J1.3, U1.5 (SDA/D1)

Board: 2 copper layers, 107 parts (0 on the bottom side), 75 nets, no tracks yet.
